pcm720/panasonic-wv-cm2080-rgb-mux/pics/result1.jpg

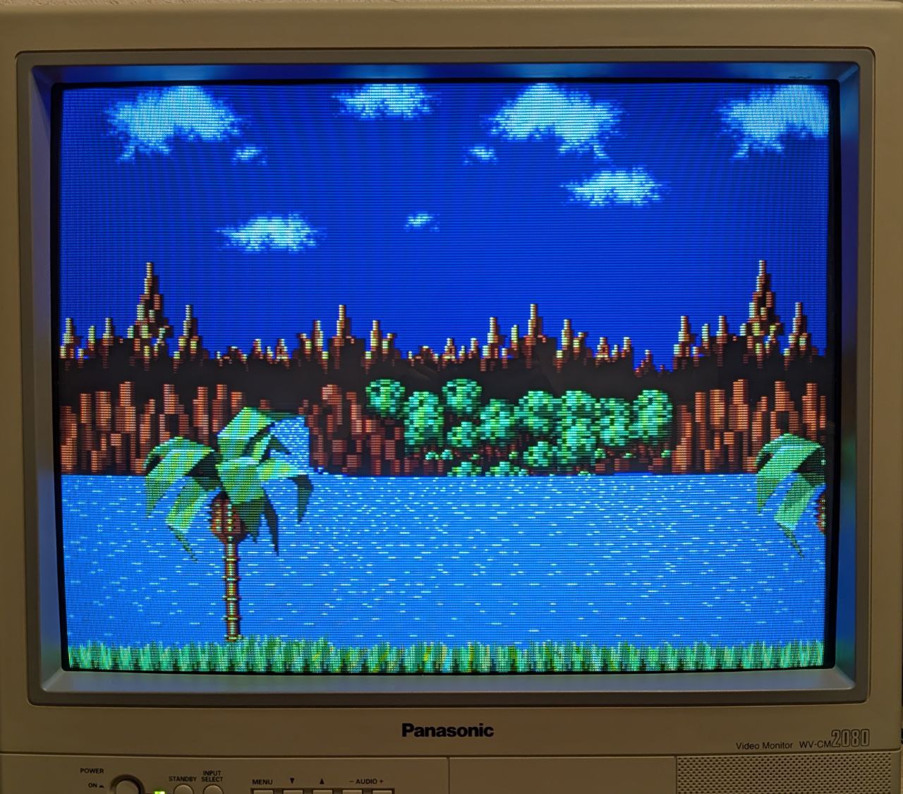
pics/result1.jpg
